kelu124/bomanz/images/20170406_124914.jpg

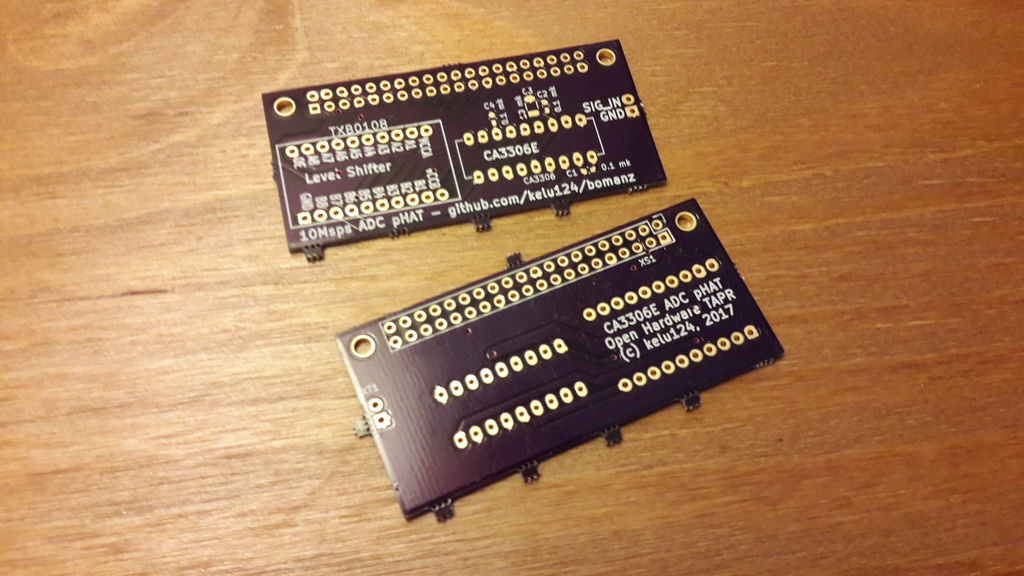
images/20170406_124914.jpg
