kelu124/bomanz/images/20170406_124950.jpg

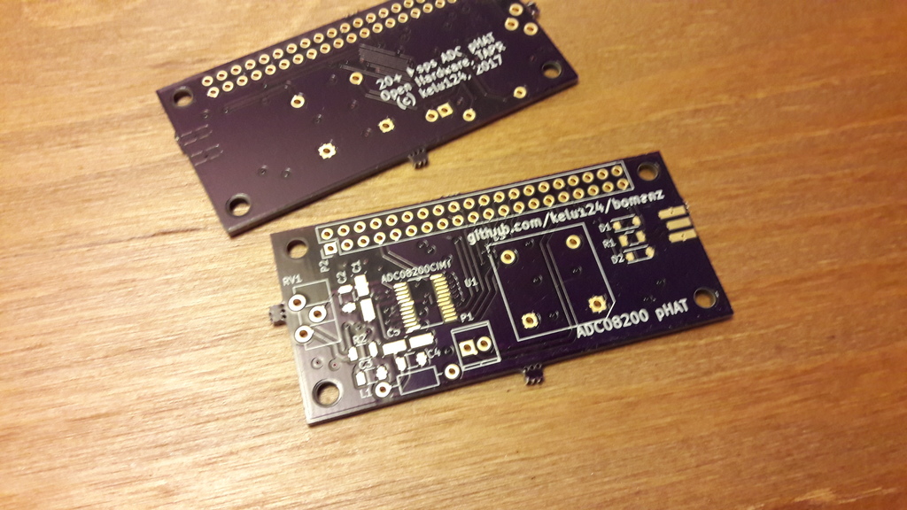
images/20170406_124950.jpg
