kelu124/bomanz/images/20170412_231408.jpg

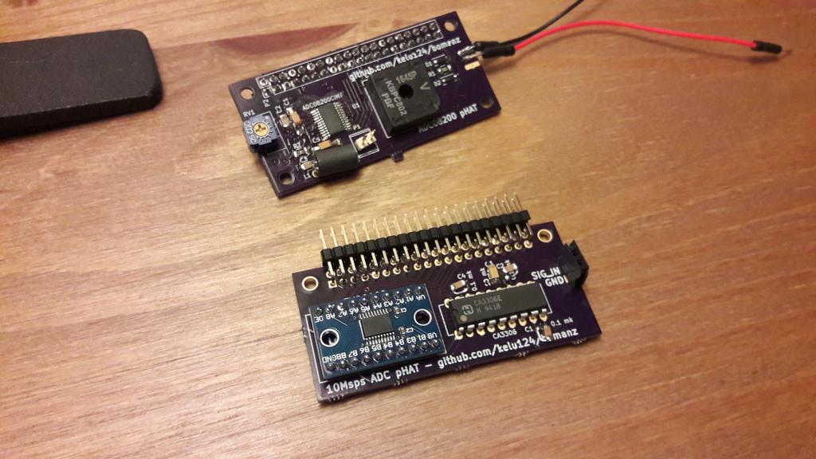
images/20170412_231408.jpg
