kelu124/bomanz/images/DifferentEnveloppes.jpg

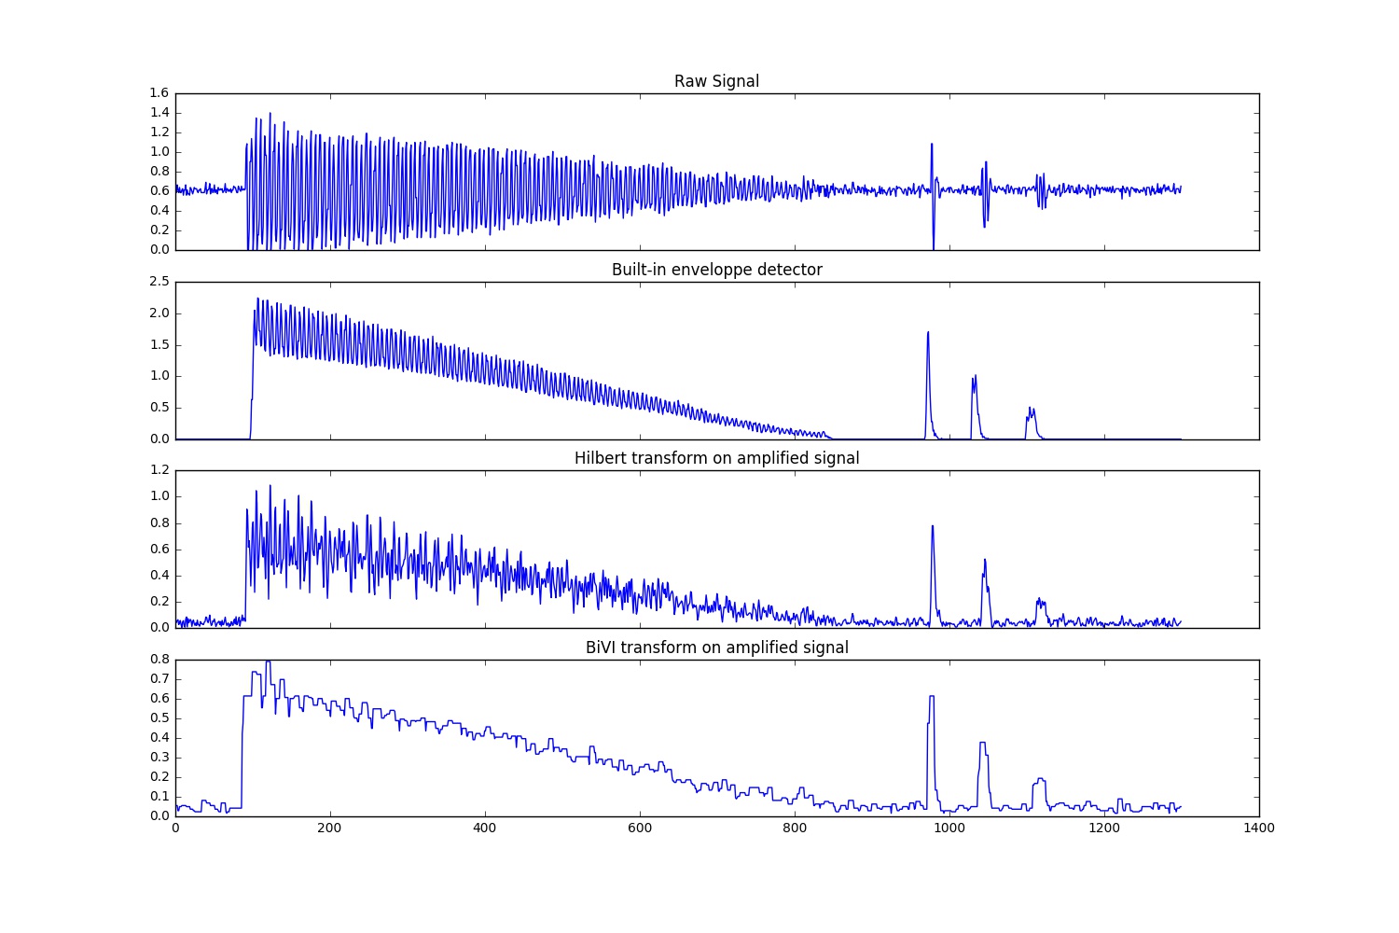
images/DifferentEnveloppes.jpg
