kelu124/bomanz/images/PiezoNoBacking.jpg

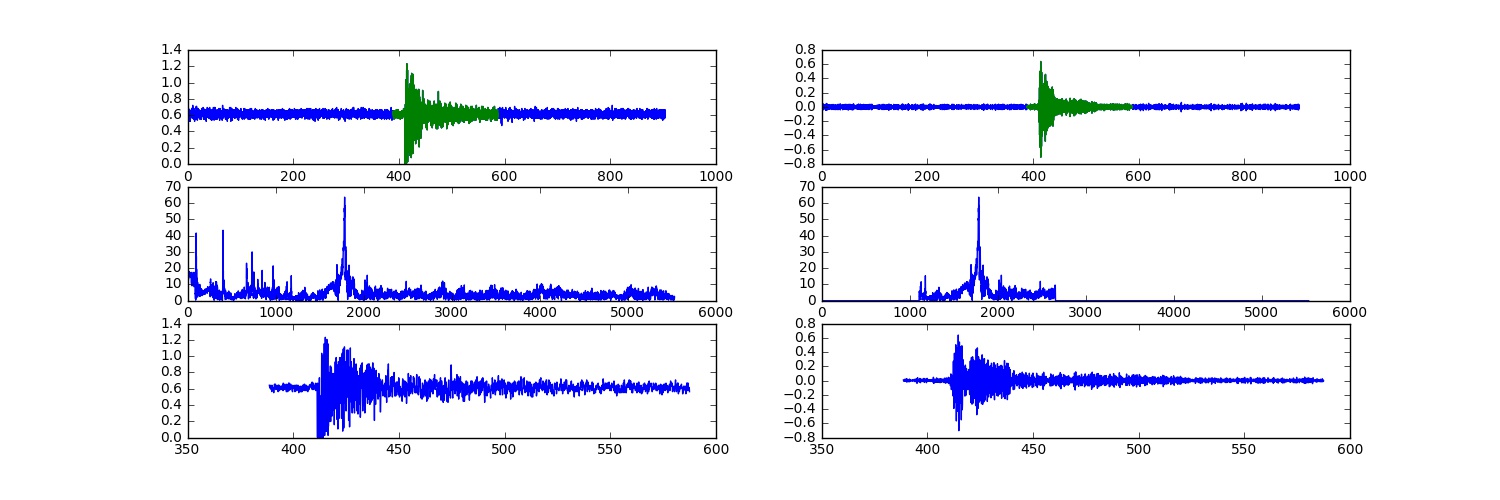
images/PiezoNoBacking.jpg
