kelu124/bomanz/images/smallOSH.png

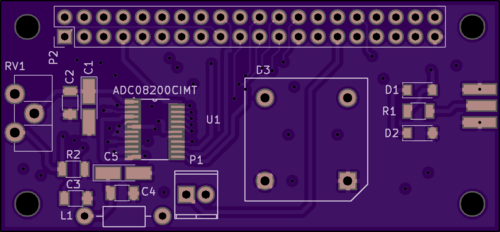
images/smallOSH.png
