kelu124/bomanz/offset/brut_GBig.JPG

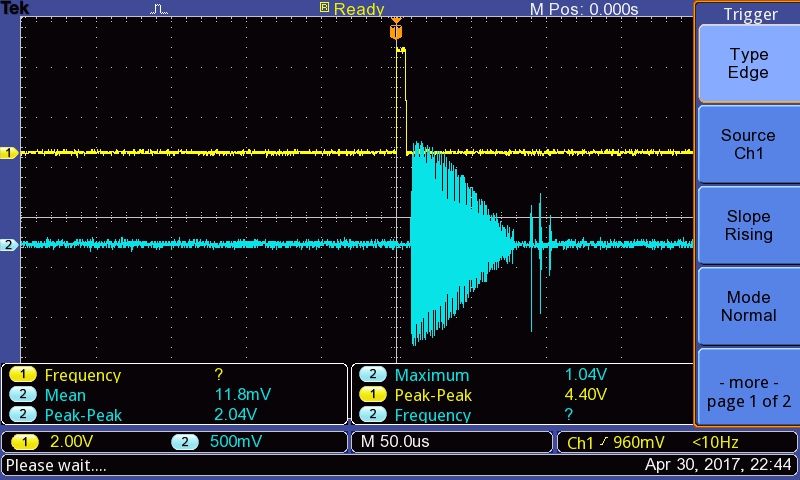
offset/brut_GBig.JPG
