kelu124/bomanz/offset/brut_GSmall.JPG

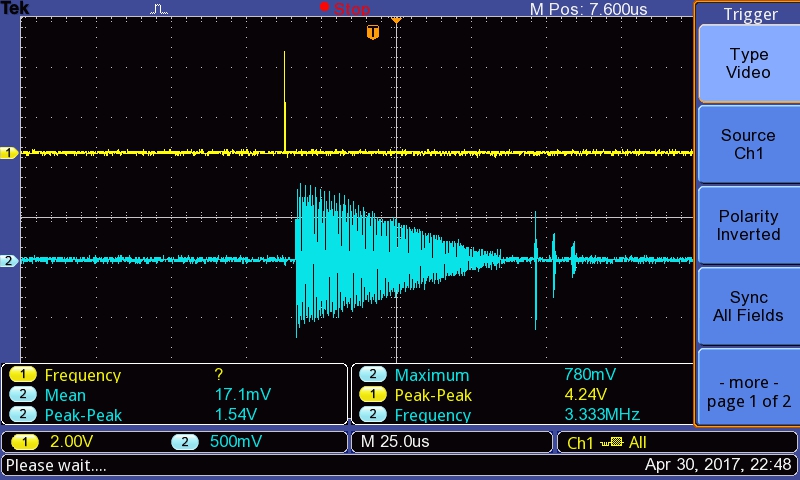
offset/brut_GSmall.JPG
