kelu124/bomanz/offset/env_GBig.JPG

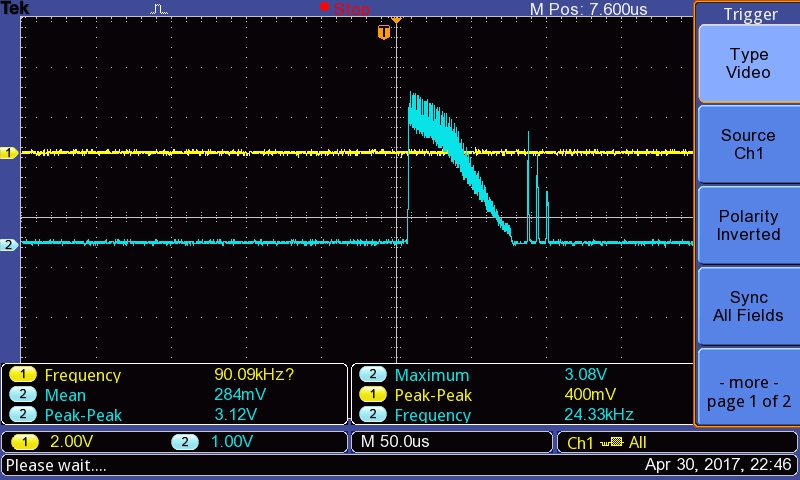
offset/env_GBig.JPG
