kelu124/bomanz/offset/env_GSmall.JPG

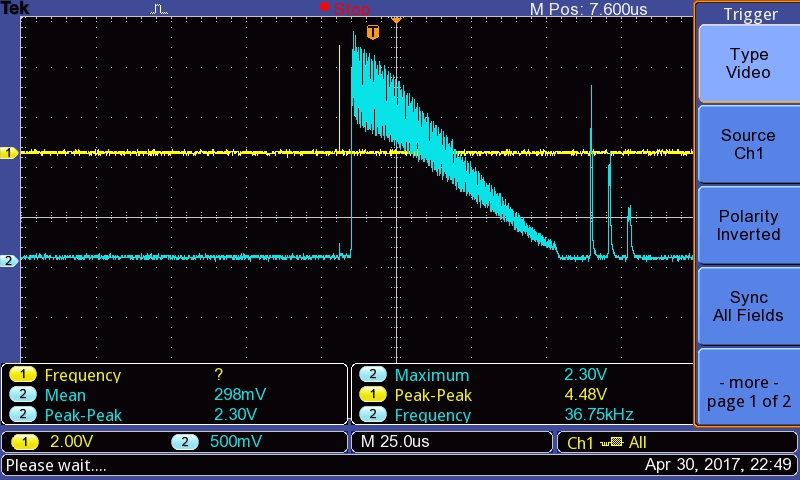
offset/env_GSmall.JPG
