kelu124/bomanz/offset/offset_sature_GBig.JPG

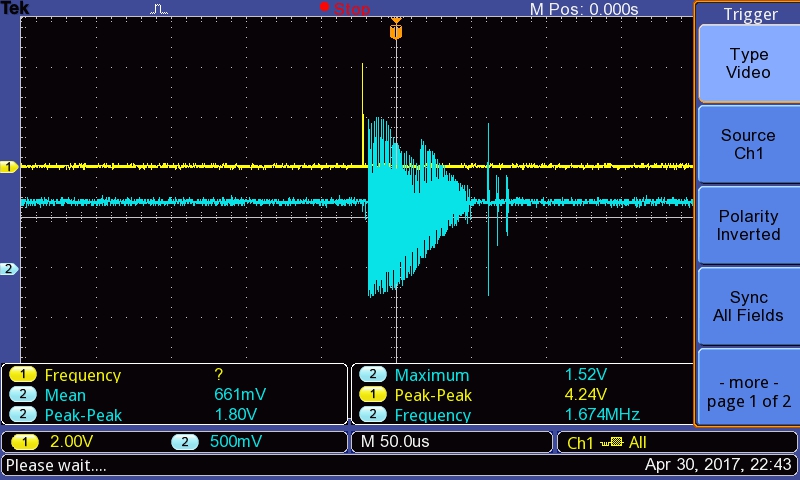
offset/offset_sature_GBig.JPG
