kelu124/bomanz/offset/SigPiezo.JPG

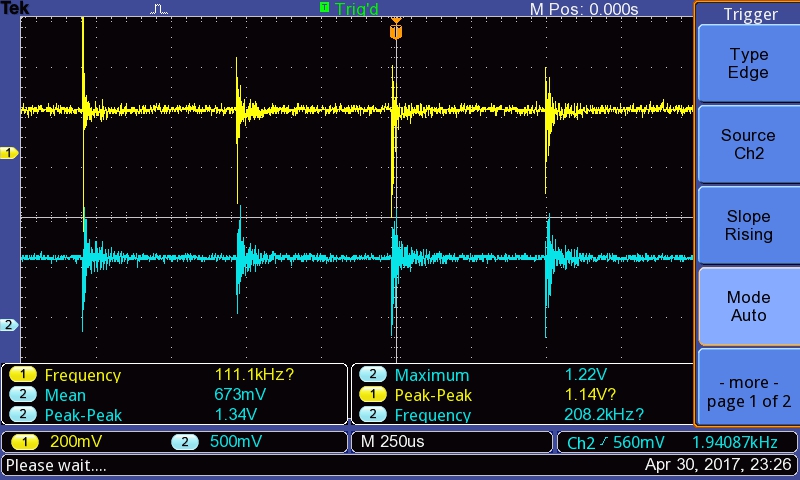
offset/SigPiezo.JPG
