kelu124/bomanz/tmp/out.c

0	0.634921	0.31746
0.0002	2.53968	2.53968
0.0004	3.01587	3.09524
0.0006	0.793651	0.396825
0.0008	0.634921	0
0.001	1.26984	0.555556
0.0012	0.47619	1.42857
0.0014	0.31746	0.238095
0.0016	1.26984	0.31746
0.0018	1.26984	1.66667
0.002	0.634921	3.80952
0.0022	0	2.93651
0.0024	2.53968	1.8254
0.0026	3.1746	0.238095
0.0028	1.26984	0.31746
0.003	3.80952	0
0.0032	0.31746	3.80952
0.0034	0	1.8254
0.0036	3.01587	4.12698
0.0038	1.5873	2.53968
0.004	1.26984	4.28571
0.0042	0	3.88889
0.0044	0	0.396825
0.0046	3.1746	2.93651
0.0048	3.01587	0.47619
0.005	2.38095	3.01587
0.0052	0.47619	1.8254
0.0054	0.634921	2.69841
0.0056	0	0.396825
0.0058	4.44444	0.555556
0.006	4.92063	4.20635
0.0062	2.22222	4.28571
0.0064	1.90476	1.26984
0.0066	2.85714	0.555556
0.0068	0.47619	1.8254
0.007	0.634921	0.15873
0.0072	0	2.93651
0.0074	3.1746	2.93651
0.0076	0.47619	0
0.0078	0.952381	4.12698
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
