kelu124/bomanz/tmp/ca3306-drv.mod.c

#include <linux/module.h>
#include <linux/vermagic.h>
#include <linux/compiler.h>

MODULE_INFO(vermagic, VERMAGIC_STRING);

__visible struct module __this_module
__attribute__((section(".gnu.linkonce.this_module"))) = {
	.name = KBUILD_MODNAME,
	.init = init_module,
#ifdef CONFIG_MODULE_UNLOAD
	.exit = cleanup_module,
#endif
	.arch = MODULE_ARCH_INIT,
};

static const struct modversion_info ____versions[]
__used
__attribute__((section("__versions"))) = {
	{ 0x5a7ba343, __VMLINUX_SYMBOL_STR(module_layout) },
	{ 0xedc03953, __VMLINUX_SYMBOL_STR(iounmap) },
	{ 0x6bc3fbc0, __VMLINUX_SYMBOL_STR(__unregister_chrdev) },
	{ 0x79c5a9f0, __VMLINUX_SYMBOL_STR(ioremap) },
	{ 0xb4fb14f7, __VMLINUX_SYMBOL_STR(__register_chrdev) },
	{ 0xbb72d4fe, __VMLINUX_SYMBOL_STR(__put_user_1) },
	{ 0xd9d10196, __VMLINUX_SYMBOL_STR(try_module_get) },
	{ 0xd697e69a, __VMLINUX_SYMBOL_STR(trace_hardirqs_on) },
	{ 0x94eea794, __VMLINUX_SYMBOL_STR(getnstimeofday64) },
	{ 0xec3d2e1b, __VMLINUX_SYMBOL_STR(trace_hardirqs_off) },
	{ 0x91715312, __VMLINUX_SYMBOL_STR(sprintf) },
	{ 0xdc58973f, __VMLINUX_SYMBOL_STR(module_put) },
	{ 0x2e5810c6, __VMLINUX_SYMBOL_STR(__aeabi_unwind_cpp_pr1) },
	{ 0x27e1a049, __VMLINUX_SYMBOL_STR(printk) },
	{ 0xb1ad28e0, __VMLINUX_SYMBOL_STR(__gnu_mcount_nc) },
};

static const char __module_depends[]
__used
__attribute__((section(".modinfo"))) =
"depends=";


MODULE_INFO(srcversion, "2BB78C4C98DE7E6BC550A1F");
